g4eml/PicoTuner/PicoTuner/dev_lowlevel_descriptors.h

/**
 * Copyright (c) 2020 Raspberry Pi (Trading) Ltd.
 *
 * SPDX-License-Identifier: BSD-3-Clause
 */

#ifndef DEV_LOWLEVEL_H_
#define DEV_LOWLEVEL_H_

#include "usb_common.h"

typedef void (*usb_ep_handler)(uint8_t *buf, uint16_t len);

// Struct in which we keep the endpoint configuration
struct usb_endpoint_configuration {
    const struct usb_endpoint_descriptor *descriptor;
    usb_ep_handler handler;

    // Pointers to endpoint + buffer control registers
    // in the USB controller DPSRAM
    volatile uint32_t *endpoint_control;
    volatile uint32_t *buffer_control;
    volatile uint8_t *data_buffer;

    // Toggle after each packet (unless replying to a SETUP)
    uint8_t next_pid;
};

// Struct in which we keep the device configuration
struct usb_device_configuration {
    const struct usb_device_descriptor *device_descriptor;
    const struct usb_interface_descriptor *interface_descriptor1;
    const struct usb_interface_descriptor *interface_descriptor2;
    const struct usb_configuration_descriptor *config_descriptor;
    const unsigned char *lang_descriptor;
    const unsigned char **descriptor_strings;
    // USB num endpoints is 16
    struct usb_endpoint_configuration endpoints[USB_NUM_ENDPOINTS];
};

#define EP0_IN_ADDR   (USB_DIR_IN  | 0)
#define EP0_OUT_ADDR  (USB_DIR_OUT | 0)
#define EP81_IN_ADDR  (USB_DIR_IN  | 1)
#define EP2_OUT_ADDR  (USB_DIR_OUT | 2)
#define EP83_IN_ADDR  (USB_DIR_IN  | 3)
#define EP84_IN_ADDR  (USB_DIR_IN  | 4)


// EP0 IN and OUT
const struct usb_endpoint_descriptor ep0_out = {
        .bLength          = sizeof(struct usb_endpoint_descriptor),
        .bDescriptorType  = USB_DT_ENDPOINT,
        .bEndpointAddress = EP0_OUT_ADDR, // EP number 0, OUT from host (rx to device)
        .bmAttributes     = USB_TRANSFER_TYPE_CONTROL,
        .wMaxPacketSize   = 64,
        .bInterval        = 0
};

const struct usb_endpoint_descriptor ep0_in = {
        .bLength          = sizeof(struct usb_endpoint_descriptor),
        .bDescriptorType  = USB_DT_ENDPOINT,
        .bEndpointAddress = EP0_IN_ADDR, // EP number 0, OUT from host (rx to device)
        .bmAttributes     = USB_TRANSFER_TYPE_CONTROL,
        .wMaxPacketSize   = 64,
        .bInterval        = 0
};

// Descriptors
const struct usb_device_descriptor device_descriptor = {
        .bLength         = sizeof(struct usb_device_descriptor),
        .bDescriptorType = USB_DT_DEVICE,
        .bcdUSB          = 0x0110, // USB 1.1 device
        .bDeviceClass    = 0,      // Specified in interface descriptor
        .bDeviceSubClass = 0,      // No subclass
        .bDeviceProtocol = 0,      // No protocol
        .bMaxPacketSize0 = 64,     // Max packet size for ep0
        .idVendor        = USBVID, // Vendor  
        .idProduct       = USBPID, // Product  
        .bcdDevice       = BCDDEVICE,      // Device revision number
        .iManufacturer   = 1,      // Manufacturer string index
        .iProduct        = 2,      // Product string index
        .iSerialNumber = 0,        // No Serial number
        .bNumConfigurations = 1    // One configuration
};

const struct usb_interface_descriptor interface_descriptor1 = {
        .bLength            = sizeof(struct usb_interface_descriptor),
        .bDescriptorType    = USB_DT_INTERFACE,
        .bInterfaceNumber   = 0,
        .bAlternateSetting  = 0,
        .bNumEndpoints      = 2,    // Interface has 2 endpoints
        .bInterfaceClass    = 0xff, // Vendor specific endpoint
        .bInterfaceSubClass = 0xff,
        .bInterfaceProtocol = 0xff,
        .iInterface         = 3
};

const struct usb_endpoint_descriptor ep81_in = {
        .bLength          = sizeof(struct usb_endpoint_descriptor),
        .bDescriptorType  = USB_DT_ENDPOINT,
        .bEndpointAddress = EP81_IN_ADDR, // EP number 1, IN to Host
        .bmAttributes     = USB_TRANSFER_TYPE_BULK,
        .wMaxPacketSize   = 64,
        .bInterval        = 0
};

const struct usb_endpoint_descriptor ep2_out = {
        .bLength          = sizeof(struct usb_endpoint_descriptor),
        .bDescriptorType  = USB_DT_ENDPOINT,
        .bEndpointAddress = EP2_OUT_ADDR, // EP number 2, Out from Host
        .bmAttributes     = USB_TRANSFER_TYPE_BULK,
        .wMaxPacketSize   = 64,
        .bInterval        = 0
};

const struct usb_interface_descriptor interface_descriptor2 = {
        .bLength            = sizeof(struct usb_interface_descriptor),
        .bDescriptorType    = USB_DT_INTERFACE,
        .bInterfaceNumber   = 1,
        .bAlternateSetting  = 0,
        .bNumEndpoints      = 2,    // Interface has 2 endpoints
        .bInterfaceClass    = 0xff, // Vendor specific endpoint
        .bInterfaceSubClass = 0xff,
        .bInterfaceProtocol = 0xff,
        .iInterface         = 4
};

const struct usb_endpoint_descriptor ep83_in = {
        .bLength          = sizeof(struct usb_endpoint_descriptor),
        .bDescriptorType  = USB_DT_ENDPOINT,
        .bEndpointAddress = EP83_IN_ADDR, // EP number 3, TS2 In to Host
        .bmAttributes     = USB_TRANSFER_TYPE_BULK,
        .wMaxPacketSize   = 64,
        .bInterval        = 0
};

const struct usb_endpoint_descriptor ep84_in = {
        .bLength          = sizeof(struct usb_endpoint_descriptor),
        .bDescriptorType  = USB_DT_ENDPOINT,
        .bEndpointAddress = EP84_IN_ADDR, // EP number 84, TS 1 In to  Host
        .bmAttributes     = USB_TRANSFER_TYPE_BULK,
        .wMaxPacketSize   = 64,
        .bInterval        = 0
};


const struct usb_configuration_descriptor config_descriptor = {
        .bLength         = sizeof(struct usb_configuration_descriptor),
        .bDescriptorType = USB_DT_CONFIG,
        .wTotalLength    = (sizeof(config_descriptor) +
                            sizeof(interface_descriptor1) +
                            sizeof(ep81_in) +
                            sizeof(ep2_out) +
                            sizeof(interface_descriptor2) +
                            sizeof(ep83_in) +
                            sizeof(ep84_in)),
        .bNumInterfaces  = 2,
        .bConfigurationValue = 1, // Configuration 1
        .iConfiguration = 0,      // No string
        .bmAttributes = 0xc0,     // attributes: self powered, no remote wakeup
        .bMaxPower = 0xFA         // 500ma
};

const unsigned char lang_descriptor[] = {
        4,         // bLength
        0x03,      // bDescriptorType == String Descriptor
        0x09, 0x04 // language id = us english
};

const unsigned char *descriptor_strings[] = {
        (unsigned char *) "BATC",    // Vendor
        (unsigned char *) "BATC PicoTuner", // Product
       (unsigned char *) "BATC PicoTuner i2c", // Interface 1
       (unsigned char *) "BATC PicoTuner TS" // Interface 2

};

#endif
